adinazugravescu/E-bookReader/Images/BATTERY(1).png

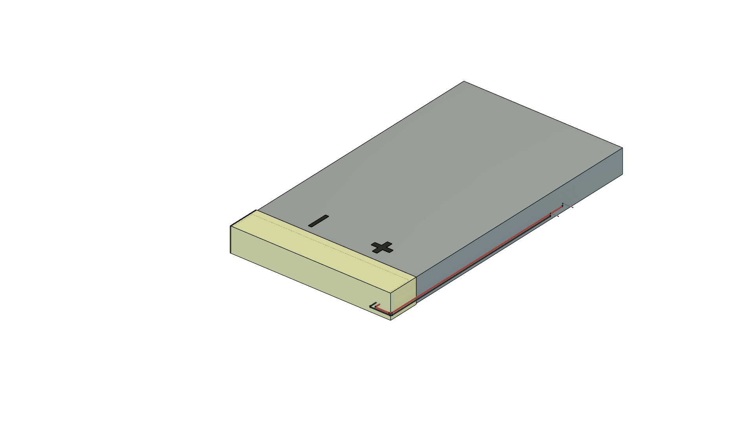
Images/BATTERY(1).png
