adinazugravescu/E-bookReader/Images/BATTERY(2).png

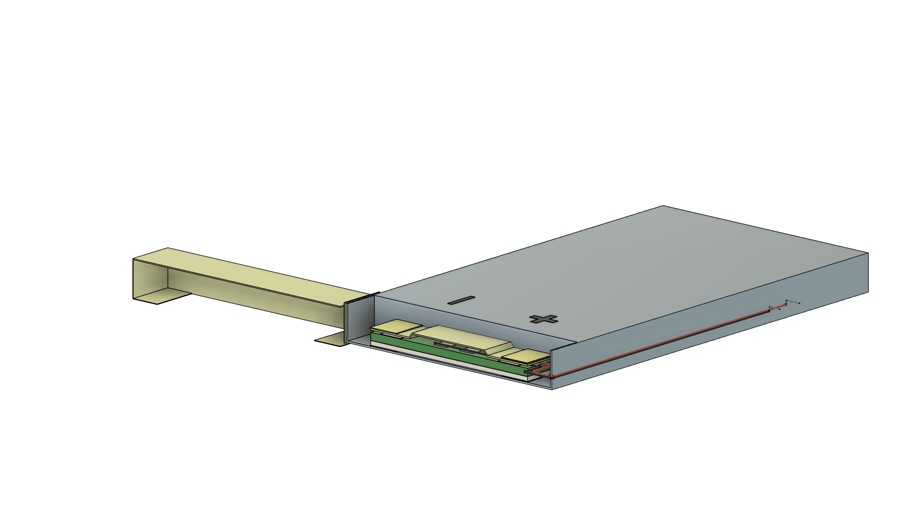
Images/BATTERY(2).png
