adinazugravescu/E-bookReader/Images/BOARD(1).png

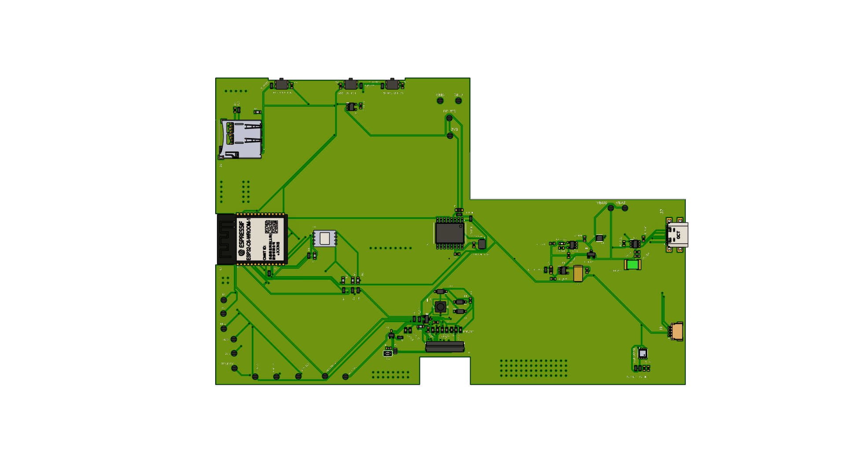
Images/BOARD(1).png
