adinazugravescu/E-bookReader/Images/BOARD(2).png

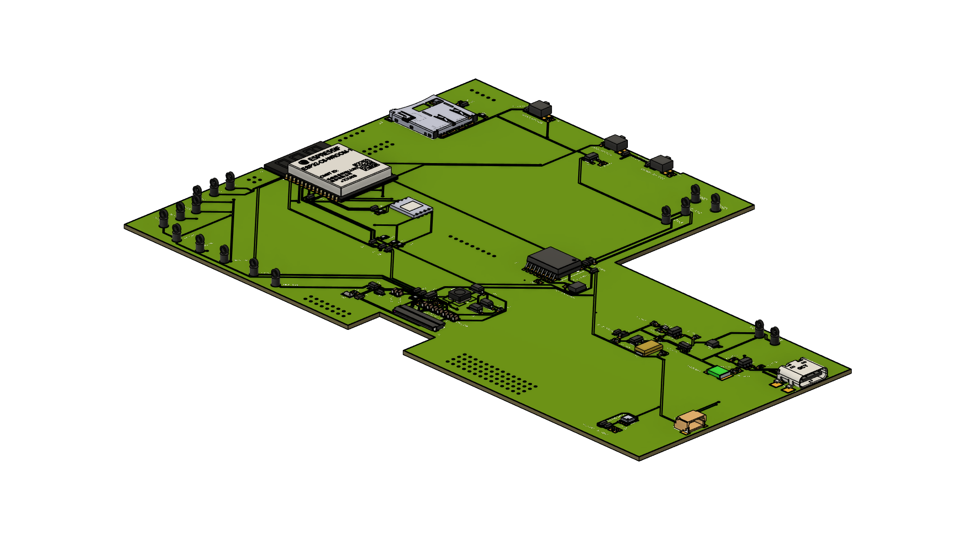
Images/BOARD(2).png
