adinazugravescu/E-bookReader/Images/DEVICE(4).png

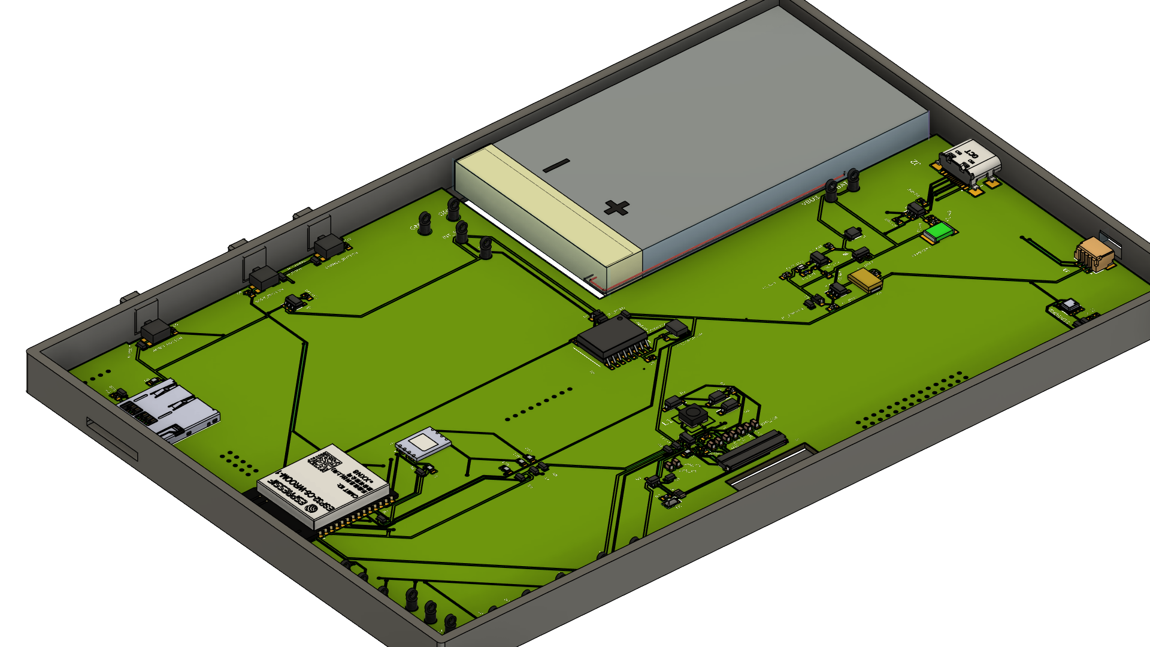
Images/DEVICE(4).png
